Peyton411/Barbell-Kinematic-Analyzer/Photo Gallery/Battery_Case_1st.png

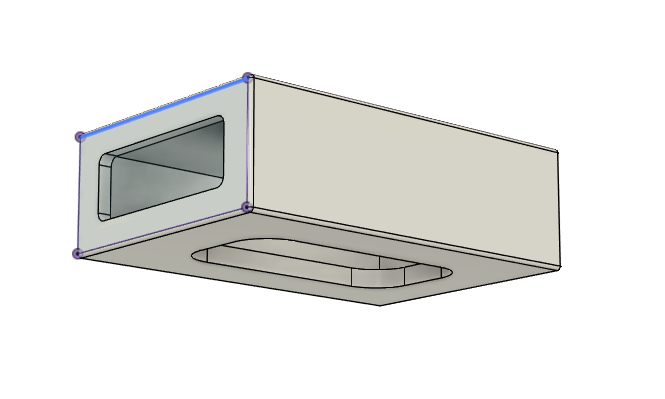
Photo Gallery/Battery_Case_1st.png
