Peyton411/Barbell-Kinematic-Analyzer/Photo Gallery/Battery_case_2.png

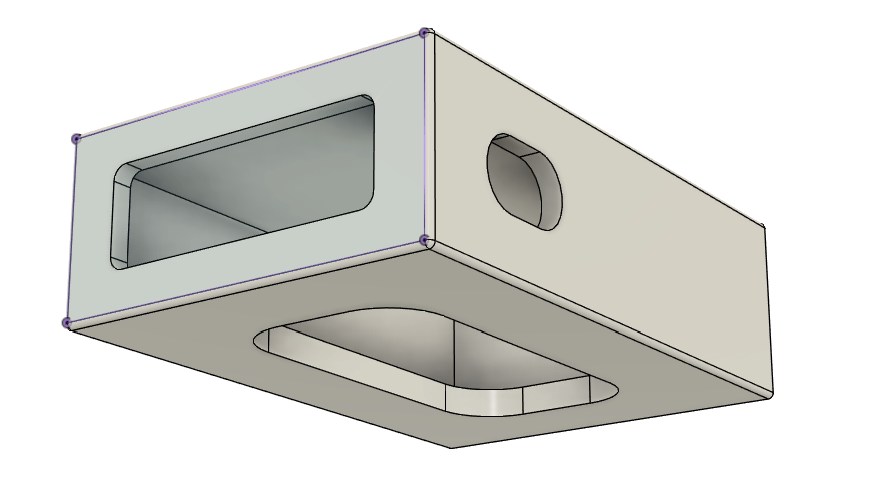
Photo Gallery/Battery_case_2.png
