Peyton411/Barbell-Kinematic-Analyzer/Photo Gallery/Battery_case_final.png

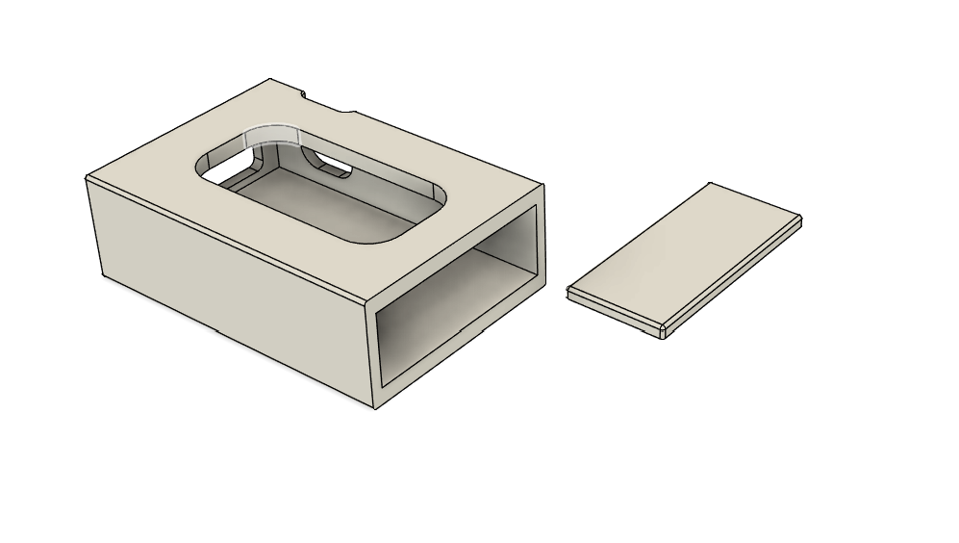
Photo Gallery/Battery_case_final.png
