Peyton411/Barbell-Kinematic-Analyzer/Photo Gallery/Collected CSV file when Still.png

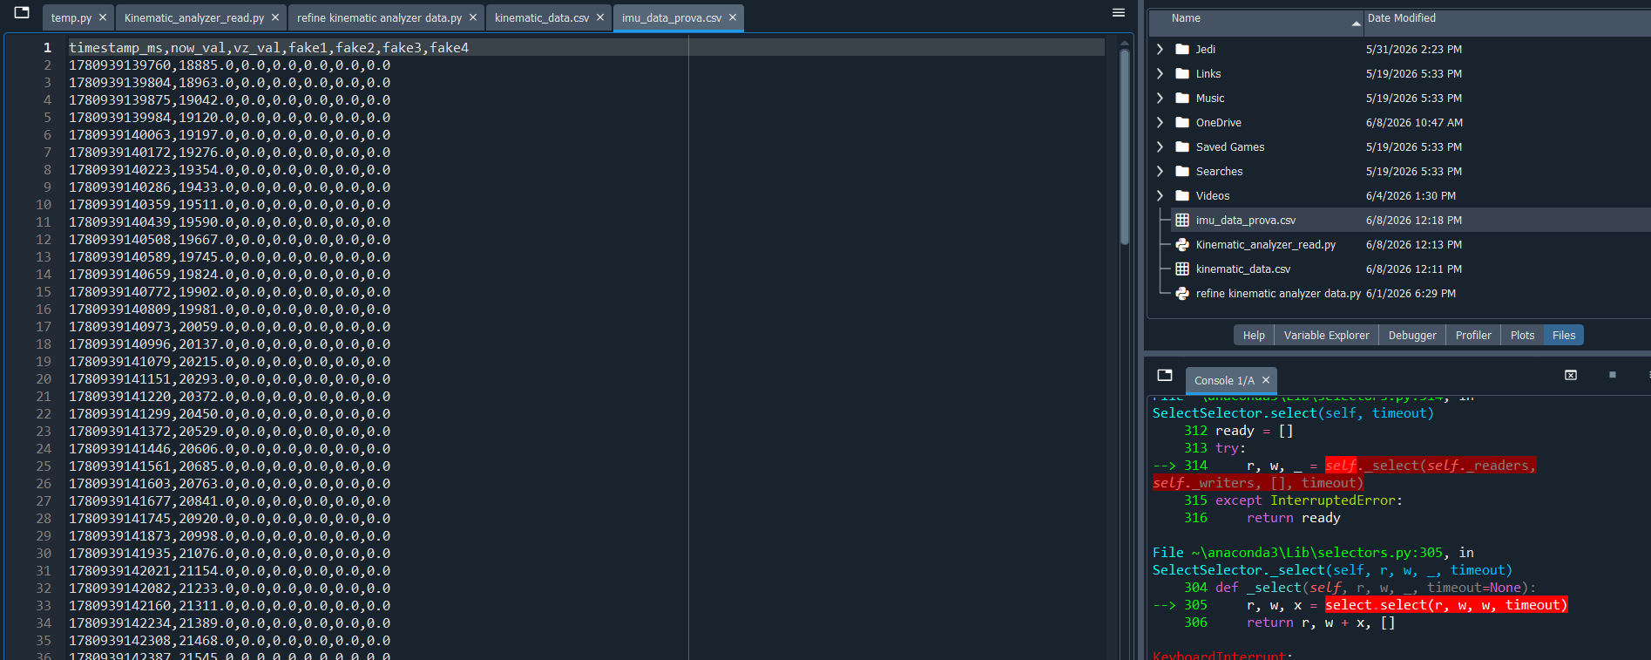
Photo Gallery/Collected CSV file when Still.png
