Peyton411/Barbell-Kinematic-Analyzer/Photo Gallery/Refined CSV file.png

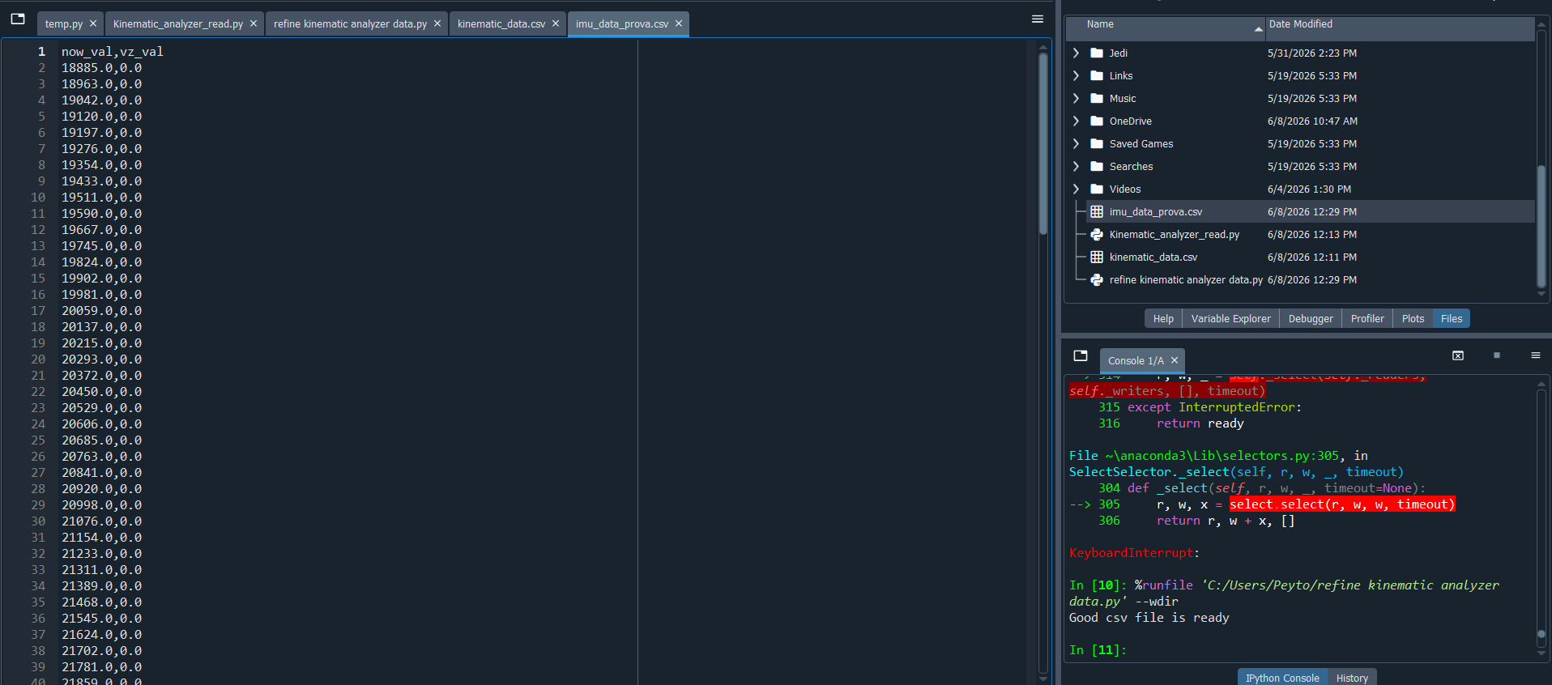
Photo Gallery/Refined CSV file.png
